SYSNET-LUMS/Batteryless-event-driven-sensing-platform/bin_depth_analysis/Images/run11_depth_avg.png

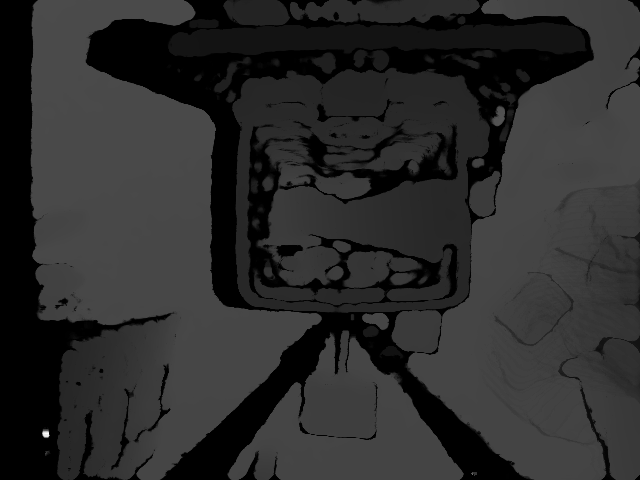
bin_depth_analysis/Images/run11_depth_avg.png
