SYSNET-LUMS/Batteryless-event-driven-sensing-platform/bin_depth_analysis/Images/run20_depth_avg.png

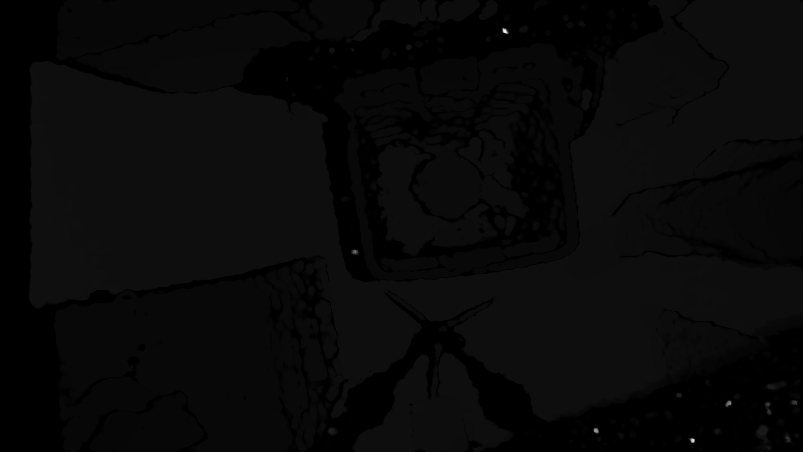
bin_depth_analysis/Images/run20_depth_avg.png
