SYSNET-LUMS/Batteryless-event-driven-sensing-platform/bin_depth_analysis/Images/run25_depth_avg.png

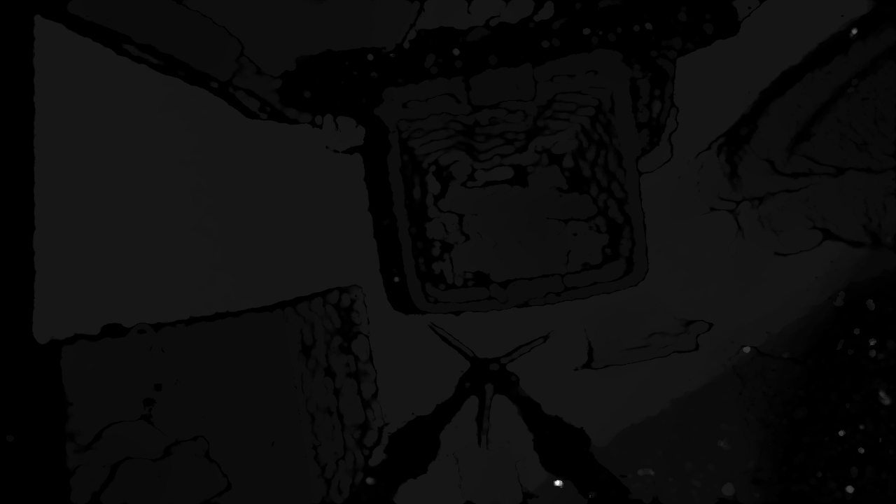
bin_depth_analysis/Images/run25_depth_avg.png
