SYSNET-LUMS/Batteryless-event-driven-sensing-platform/bin_depth_analysis/Images/run42_rgb_avg.png

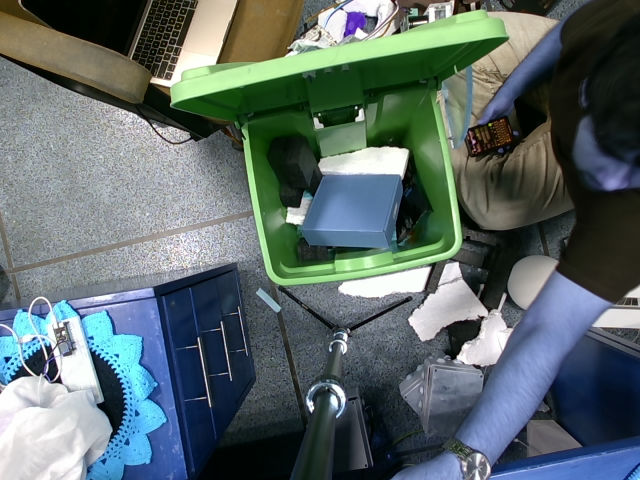
bin_depth_analysis/Images/run42_rgb_avg.png
