SYSNET-LUMS/Batteryless-event-driven-sensing-platform/bin_depth_analysis/Images/run44_rgb_avg.png

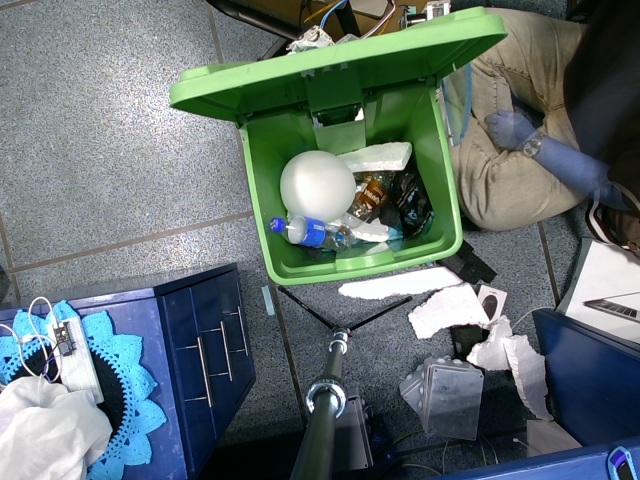
bin_depth_analysis/Images/run44_rgb_avg.png
