SYSNET-LUMS/Batteryless-event-driven-sensing-platform/bin_depth_analysis/Wall Masks/run7_depth_avg.png

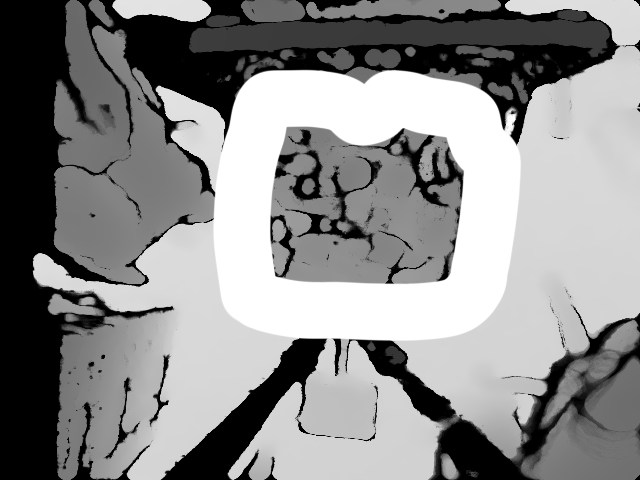
bin_depth_analysis/Wall Masks/run7_depth_avg.png
