SYSNET-LUMS/Batteryless-event-driven-sensing-platform/media/images/cabinet-unit/20260430_194214~2.jpg.jpeg

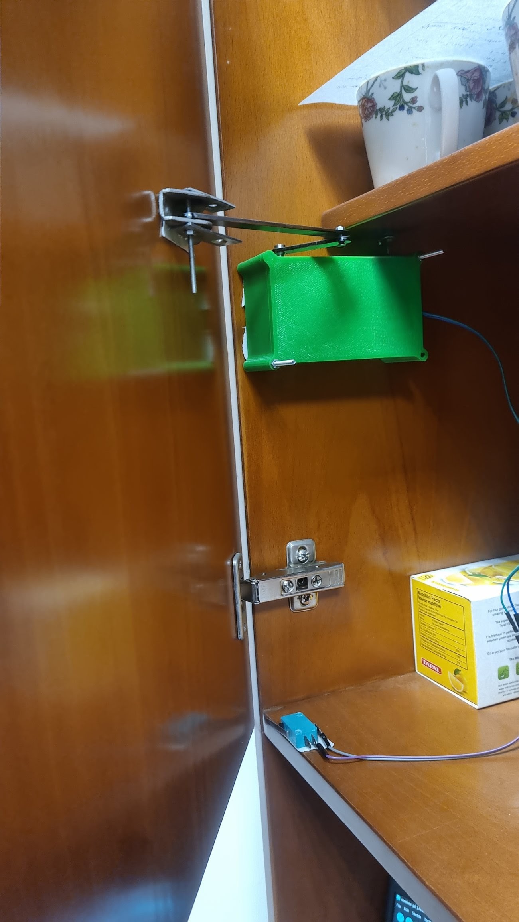
media/images/cabinet-unit/20260430_194214~2.jpg.jpeg
