SYSNET-LUMS/Batteryless-event-driven-sensing-platform/media/images/cabinet-unit/20260430_195602~2.jpg.jpeg

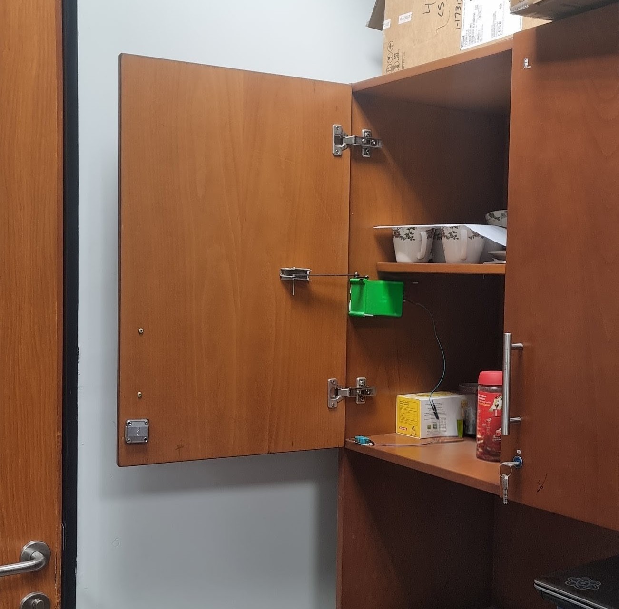
media/images/cabinet-unit/20260430_195602~2.jpg.jpeg
