SYSNET-LUMS/Batteryless-event-driven-sensing-platform/media/images/door-unit/20260503_033846~2.jpg.jpeg

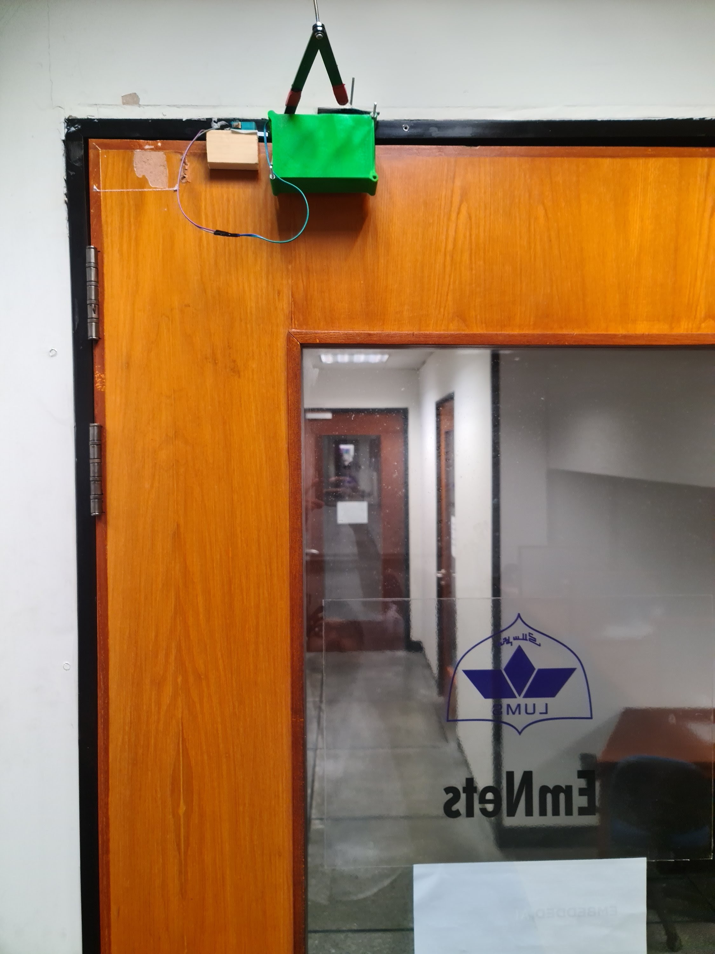
media/images/door-unit/20260503_033846~2.jpg.jpeg
