SYSNET-LUMS/Batteryless-event-driven-sensing-platform/bin_depth_analysis/results/run_outputs/run18_output_1.png

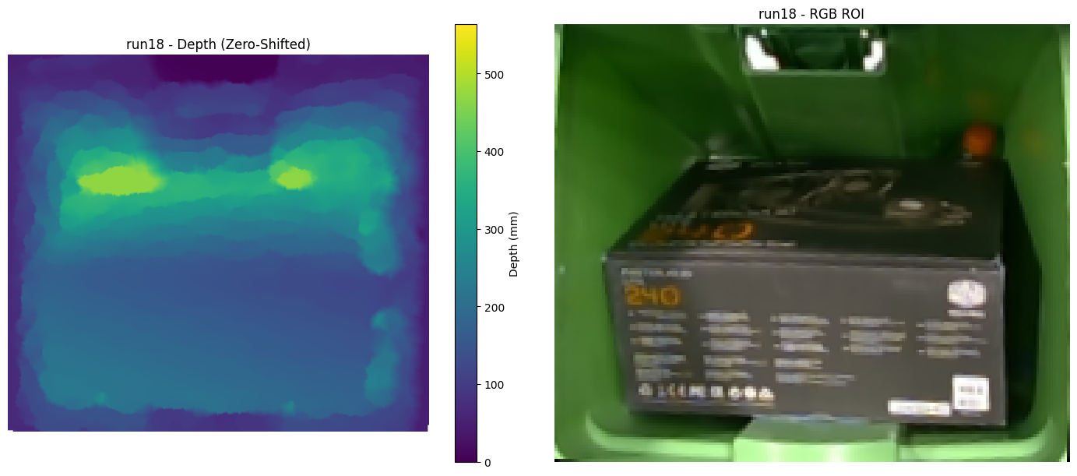
bin_depth_analysis/results/run_outputs/run18_output_1.png
