SYSNET-LUMS/Batteryless-event-driven-sensing-platform/bin_depth_analysis/results/run_outputs/run49_output_1.png

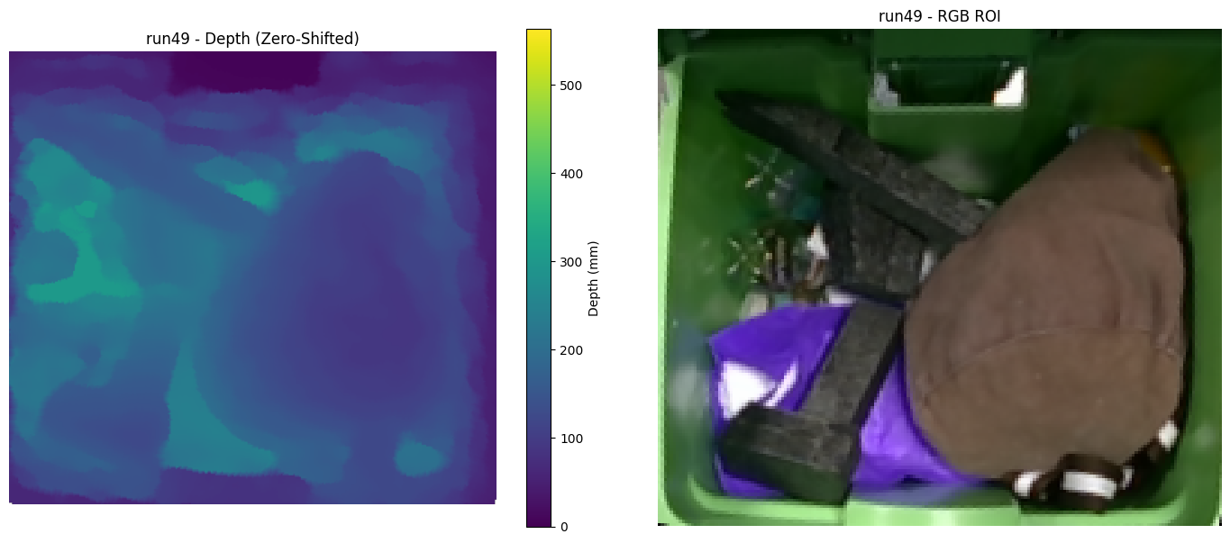
bin_depth_analysis/results/run_outputs/run49_output_1.png
