SYSNET-LUMS/Batteryless-event-driven-sensing-platform/media/images/bin-unit/20260204_154052.jpg

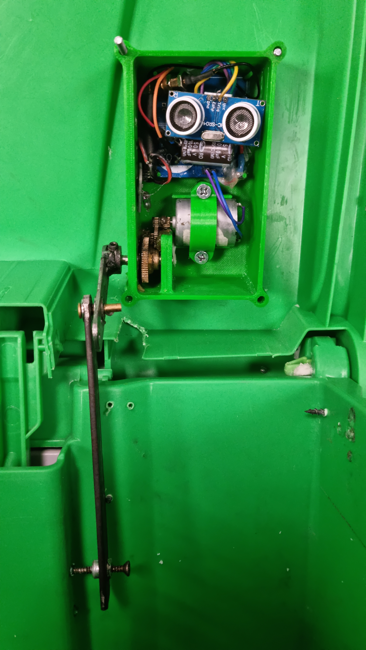
media/images/bin-unit/20260204_154052.jpg
