SYSNET-LUMS/Batteryless-event-driven-sensing-platform/media/images/bin-unit/20260204_154053.jpg

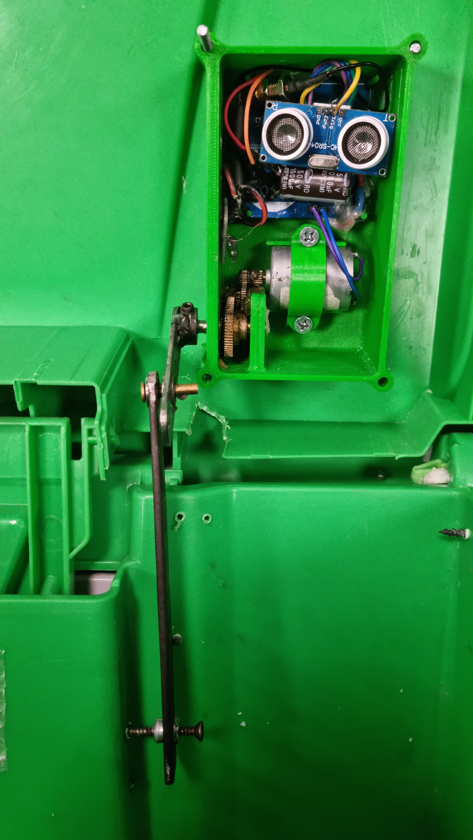
media/images/bin-unit/20260204_154053.jpg
