SYSNET-LUMS/Batteryless-event-driven-sensing-platform/media/images/bin-unit/20260204_154154.jpg

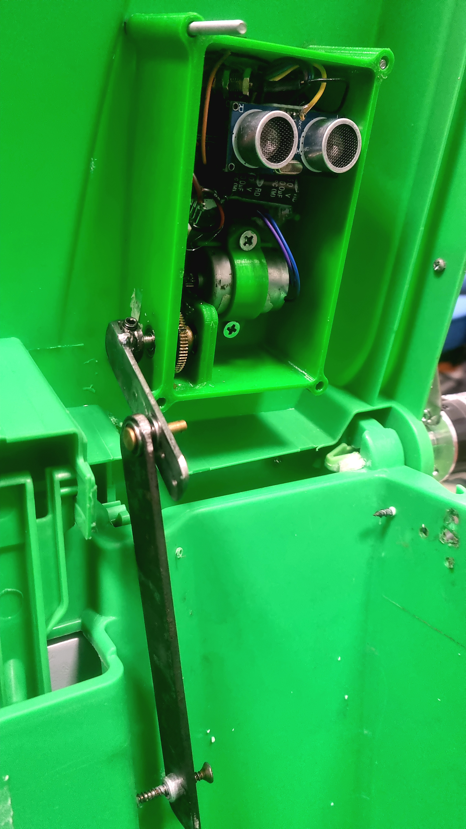
media/images/bin-unit/20260204_154154.jpg
