SYSNET-LUMS/Batteryless-event-driven-sensing-platform/media/images/bin-unit/20260204_154224.jpg

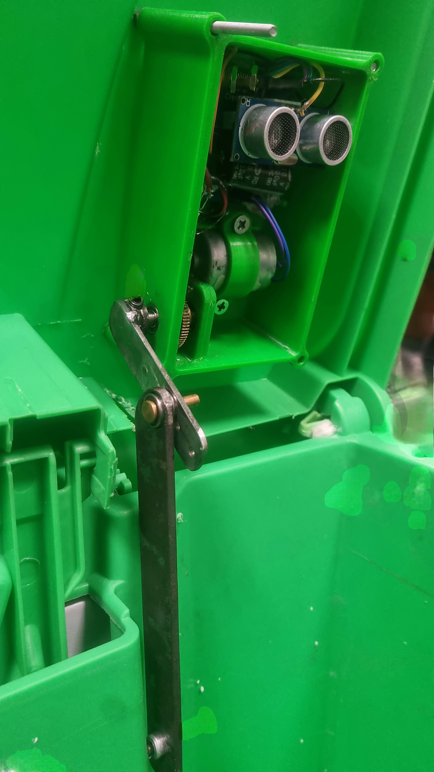
media/images/bin-unit/20260204_154224.jpg
